monkalynn813/Haptic_feedback_of_whisking/media/AP_success.png

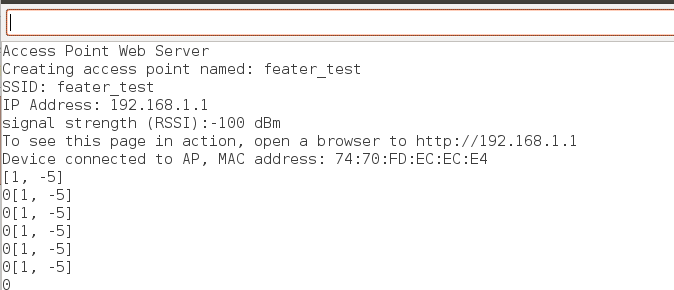
media/AP_success.png
