monkalynn813/Haptic_feedback_of_whisking/media/IMG_3164.jpg

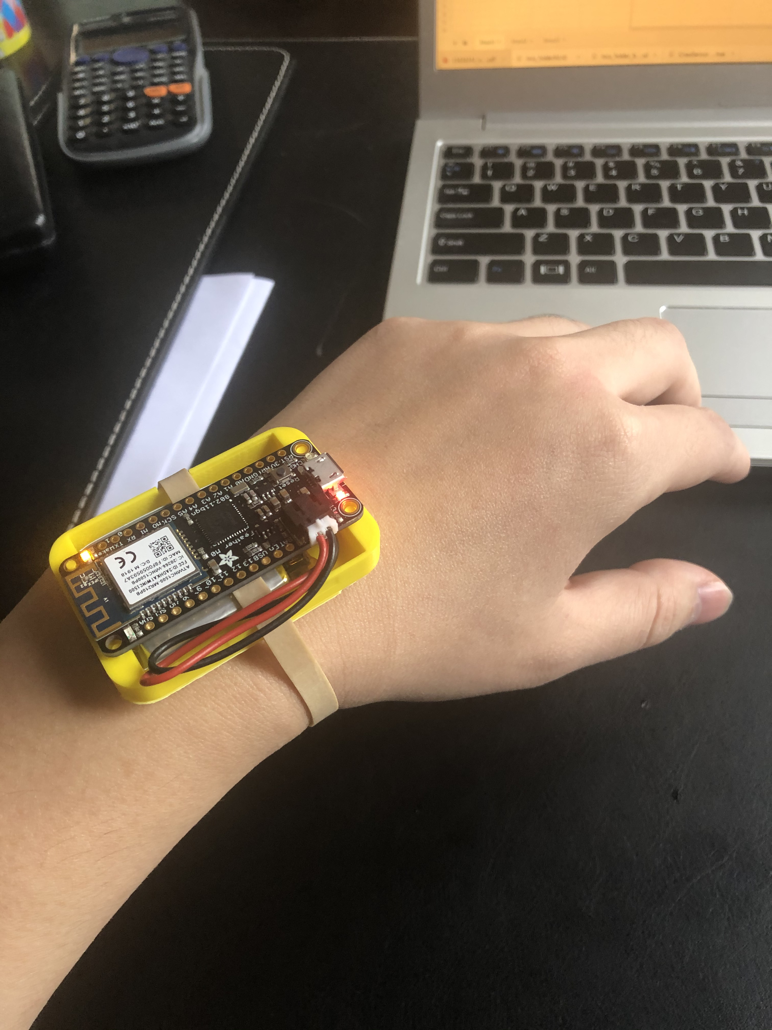
media/IMG_3164.jpg
